Maxolus/AnonTUI/unity/MoTUI-Simulation/Assets/YawVR/Sample/Arcade_Car_Physics/Models/Wheel01.obj

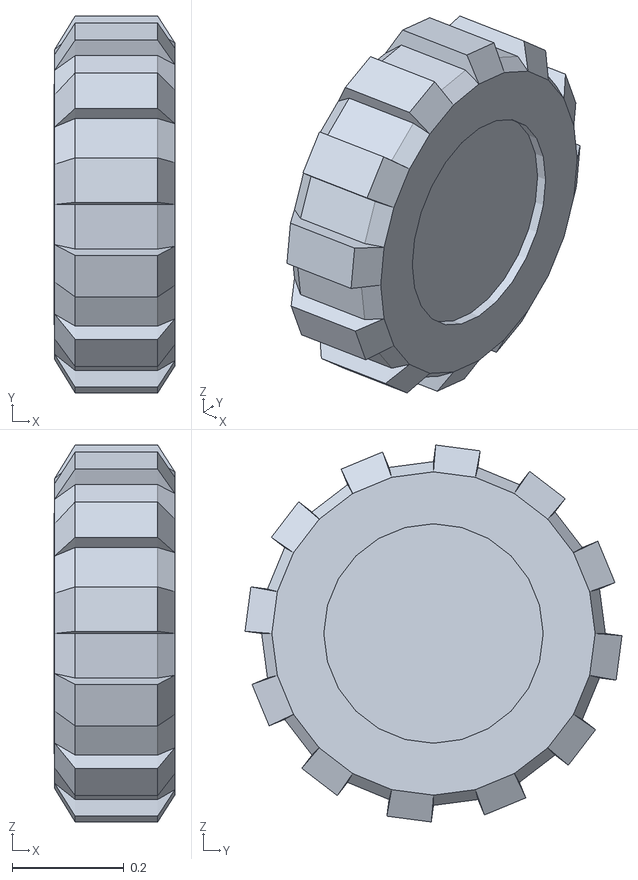
[picture p33: CAD file, 2026-03-25]
unity/MoTUI-Simulation/Assets/YawVR/Sample/Arcade_Car_Physics/Models/Wheel01.obj
0.216 x 0.676 x 0.676
