Maxolus/AnonTUI/3D Printing - STL Files/Button/top texture test.stl

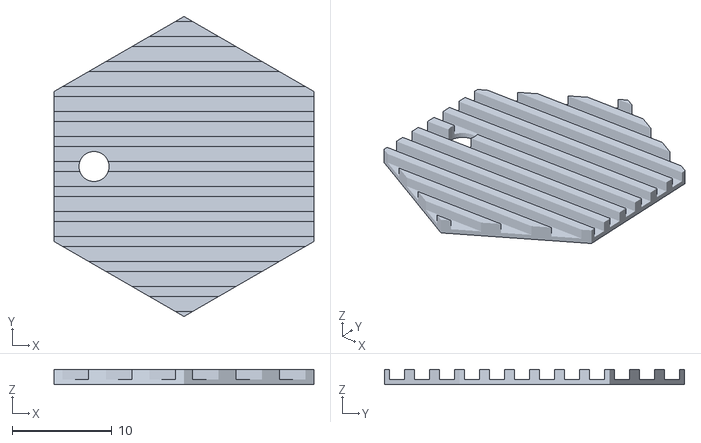
[picture p34: CAD file, 2026-03-25]
3D Printing - STL Files/Button/top texture test.stl
26.0 x 30.0 x 1.50
