Maxolus/AnonTUI/3D Printing - STL Files/Dupont Cable/18_Pin_Top.stl

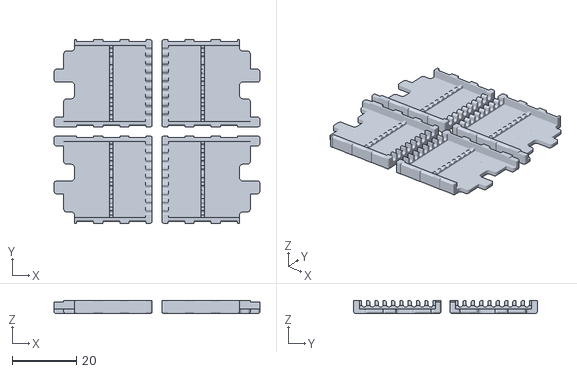
[picture p35: CAD file, 2026-03-25]
3D Printing - STL Files/Dupont Cable/18_Pin_Top.stl
64.2 x 57.2 x 4.08
