Maxolus/AnonTUI/3D Printing - STL Files/LED Elemente/Triangle.stl

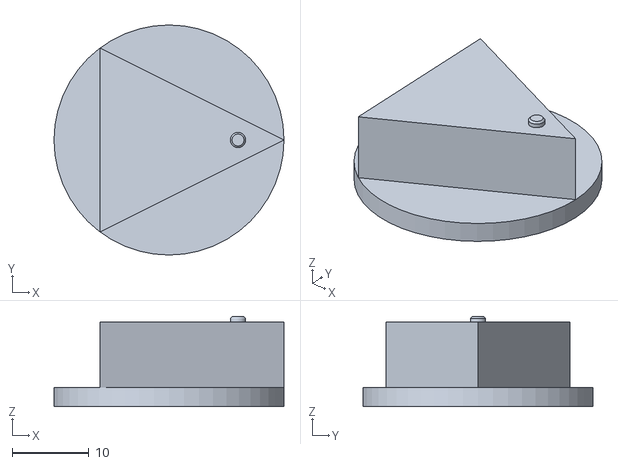
[picture p36: CAD file, 2026-03-25]
3D Printing - STL Files/LED Elemente/Triangle.stl
30.0 x 30.0 x 11.8
