Maxolus/AnonTUI/3D Printing - STL Files/Linear/linear Guide.stl

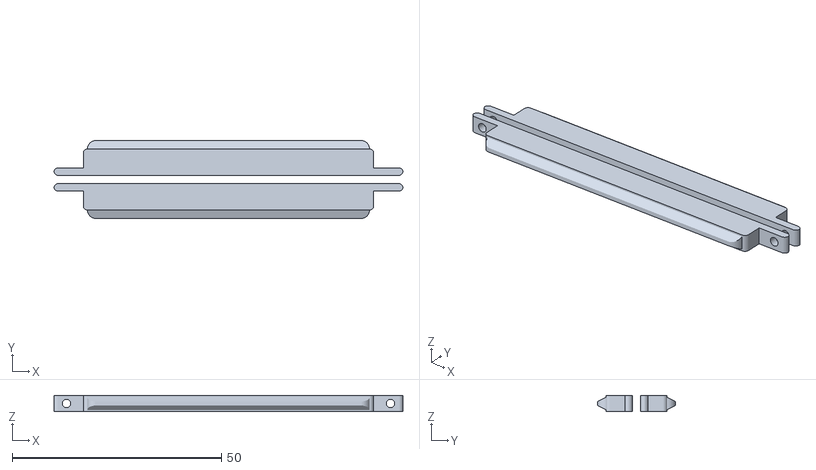
[picture p37: CAD file, 2026-03-25]
3D Printing - STL Files/Linear/linear Guide.stl
83.4 x 18.6 x 3.83
