Maxolus/AnonTUI/3D Printing - STL Files/Rotation/rotation Clip.stl

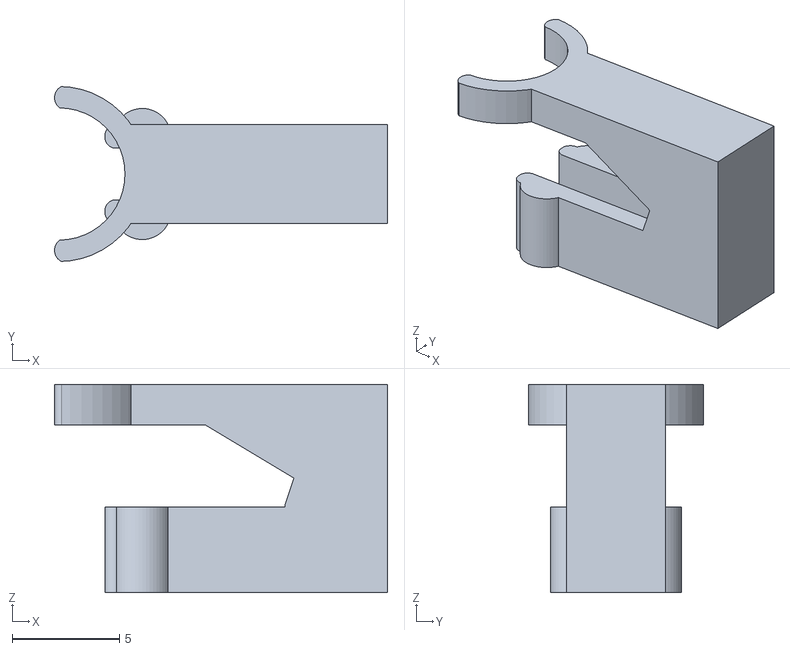
[picture p38: CAD file, 2026-03-25]
3D Printing - STL Files/Rotation/rotation Clip.stl
15.5 x 8.13 x 9.70
