Maxolus/AnonTUI/3D Printing - STL Files/Vertical/Cam Flat.stl

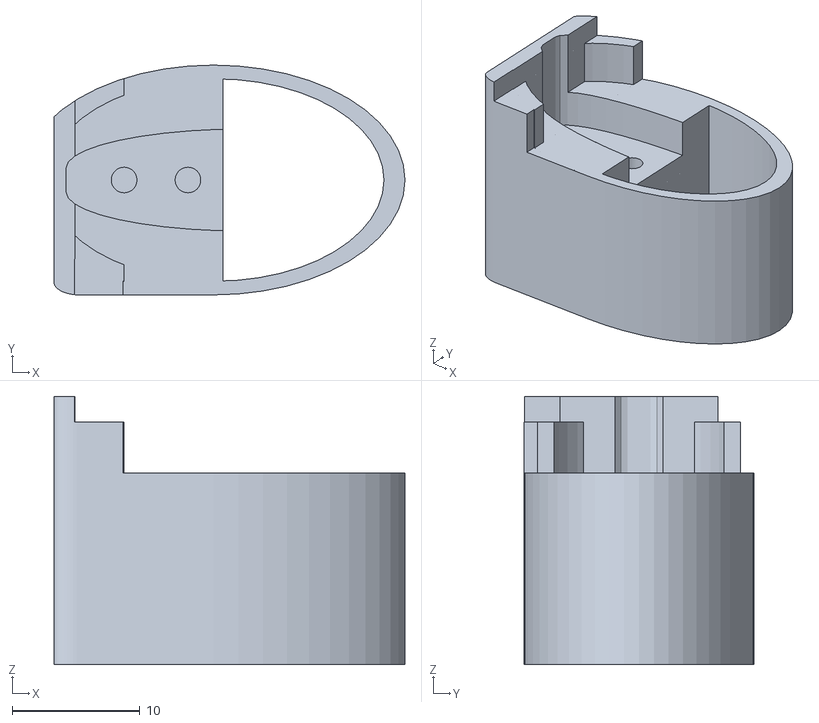
[picture p39: CAD file, 2026-03-25]
3D Printing - STL Files/Vertical/Cam Flat.stl
27.5 x 18.0 x 21.0
