Maxolus/AnonTUI/3D Printing - STL Files/Button/but bottom.stl

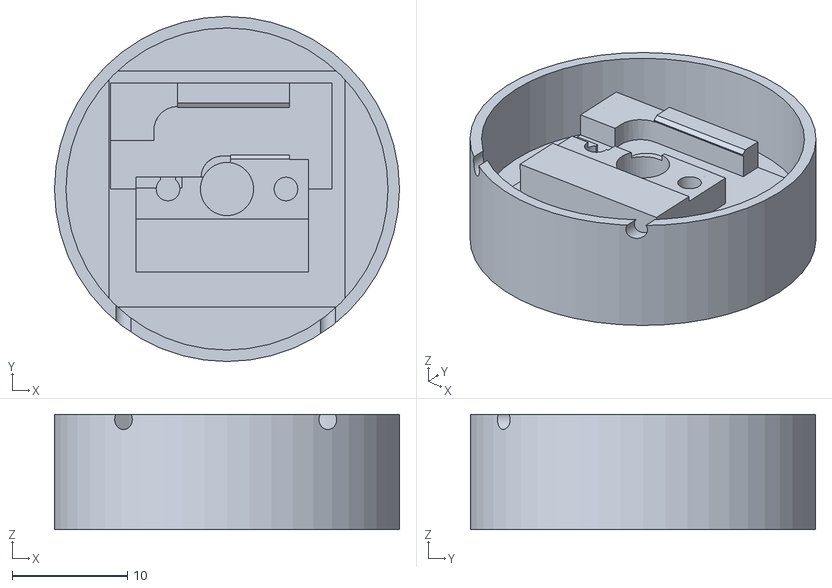
[picture p40: CAD file, 2026-03-25]
3D Printing - STL Files/Button/but bottom.stl
30.0 x 30.0 x 10.0
