Maxolus/AnonTUI/3D Printing - STL Files/Linear/linear Gear Small.stl

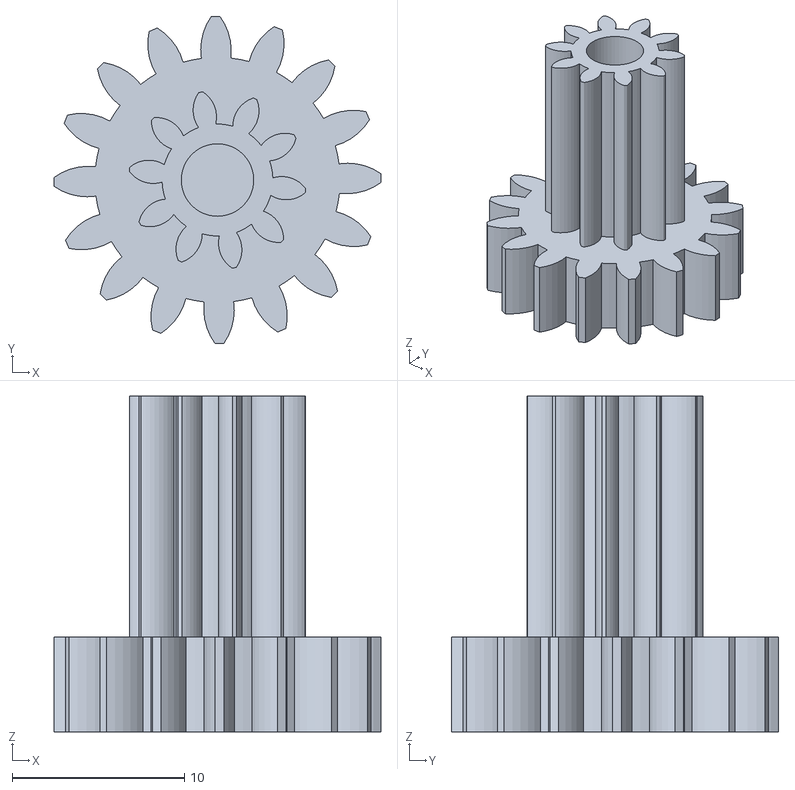
[picture p41: CAD file, 2026-03-25]
3D Printing - STL Files/Linear/linear Gear Small.stl
19.0 x 19.0 x 19.5
