Maxolus/AnonTUI/3D Printing - STL Files/Linear/linear Straight Gear.stl

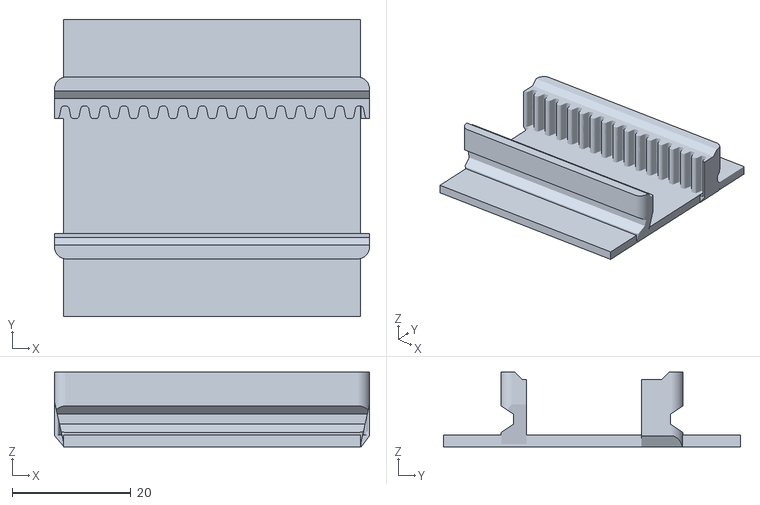
[picture p42: CAD file, 2026-03-25]
3D Printing - STL Files/Linear/linear Straight Gear.stl
53.0 x 50.0 x 12.6
